jbilander/ReAgnus/images/screenshot_pic6.png

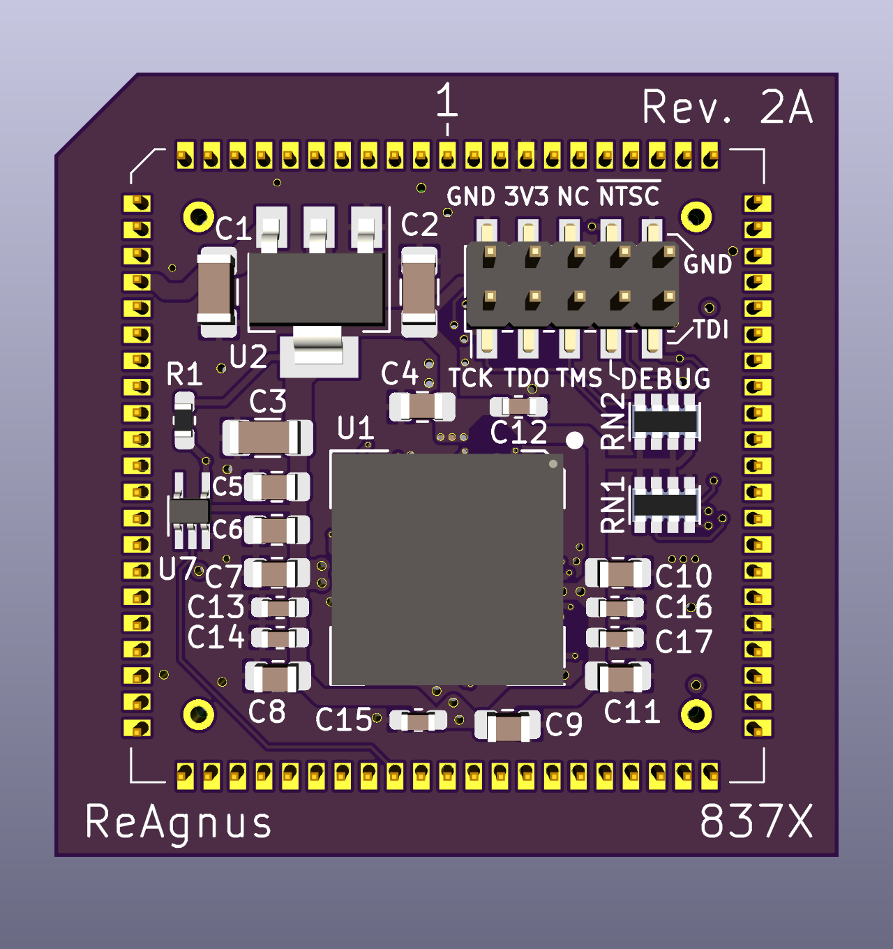
images/screenshot_pic6.png
