jbilander/ReAgnus/images/screenshot_pic7.png

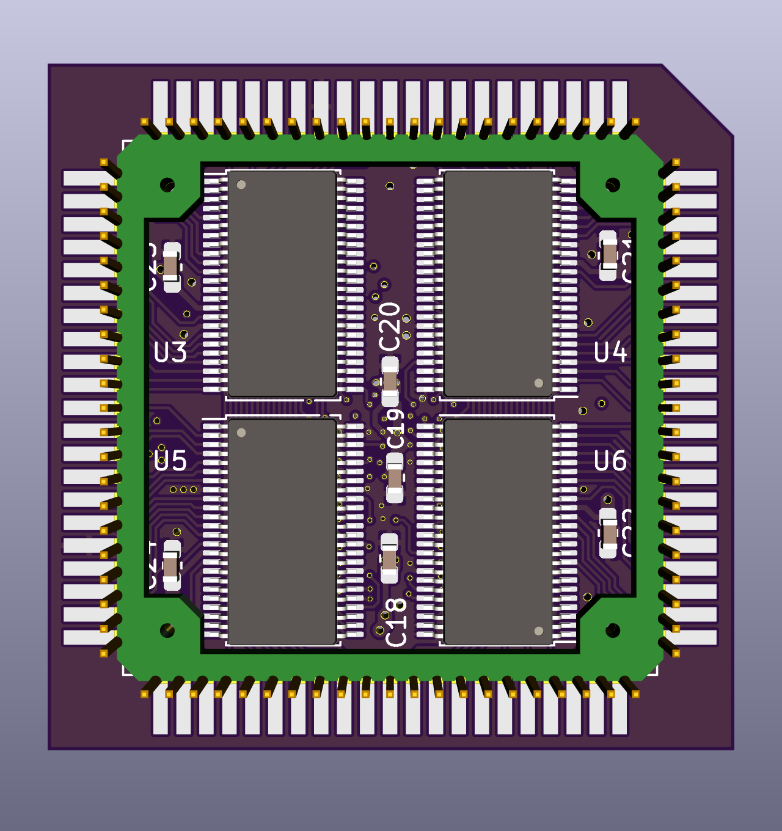
images/screenshot_pic7.png
