jbilander/ReAgnus/images/screenshot_pic8.png

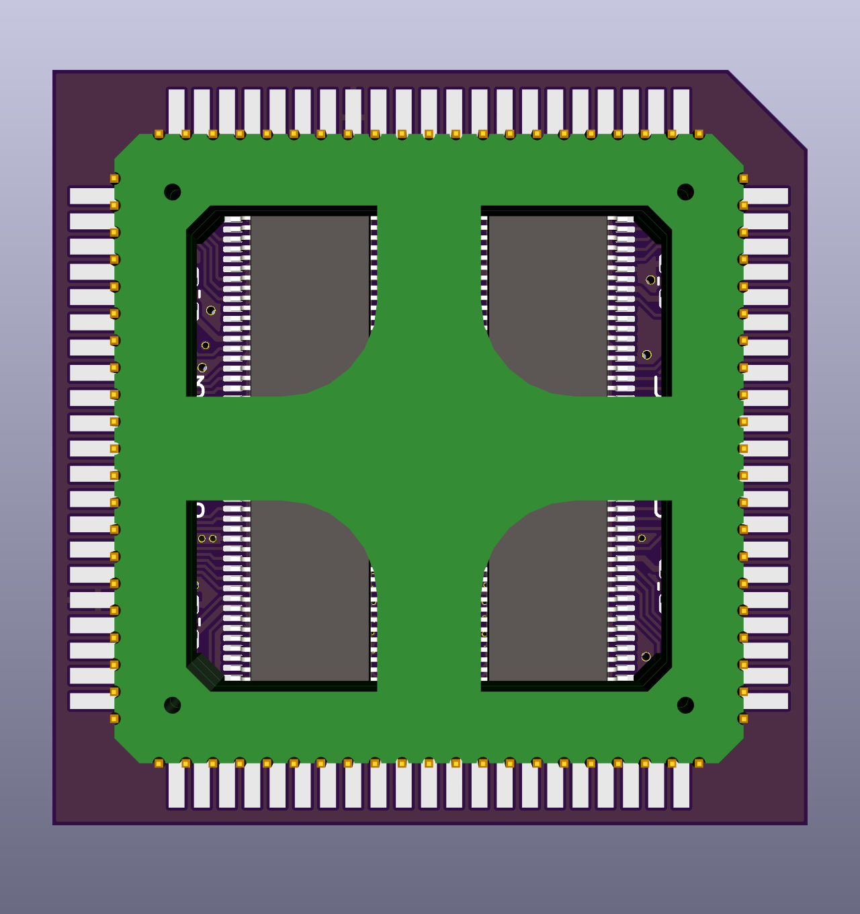
images/screenshot_pic8.png
